nislamovs/Hardware-htop/docs/arduino_ide.png

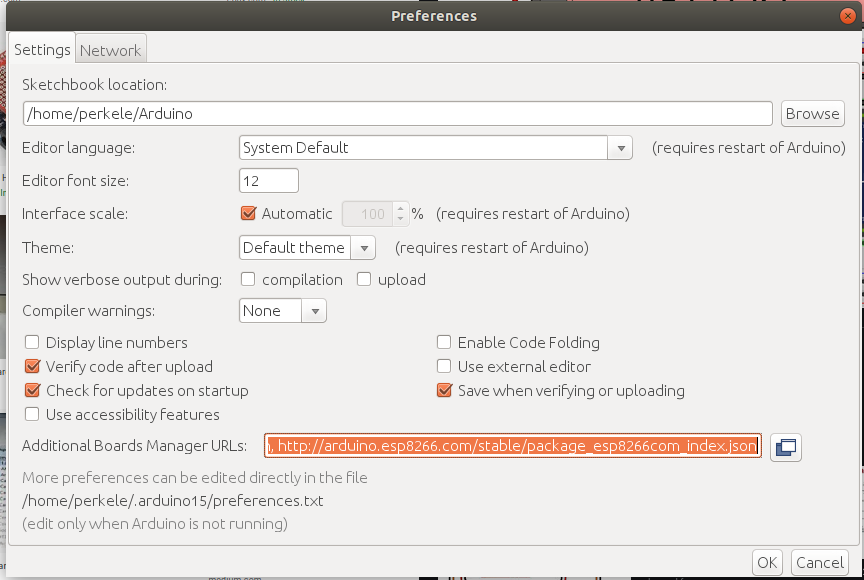
docs/arduino_ide.png
