nislamovs/Hardware-htop/docs/PURPOSE.JPG

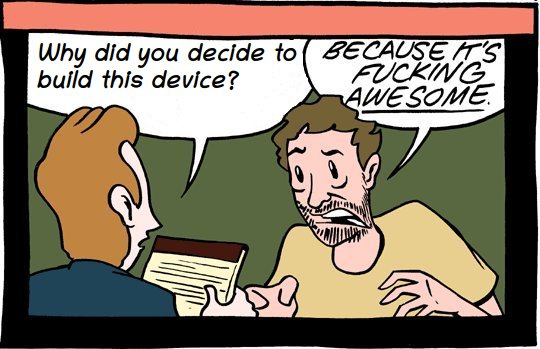
docs/PURPOSE.JPG
