nislamovs/Hardware-htop/front_panel_images/Core_01_bottom.png

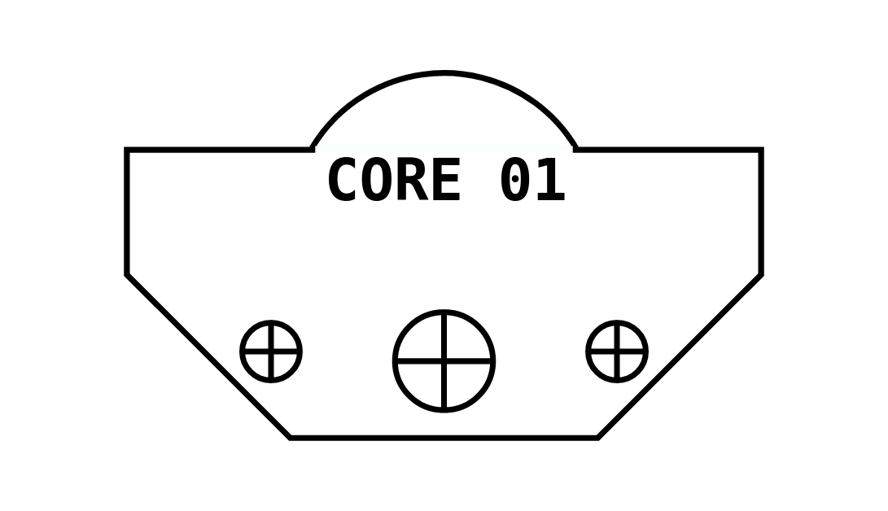
front_panel_images/Core_01_bottom.png
