nislamovs/Hardware-htop/front_panel_images/Core_all_top.png

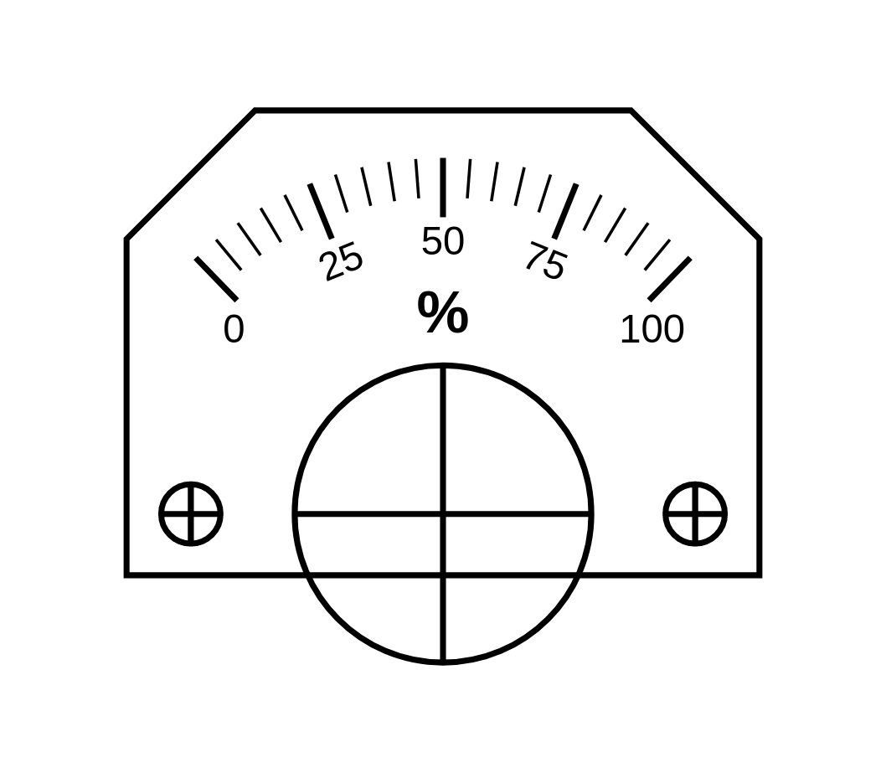
front_panel_images/Core_all_top.png
