nislamovs/Hardware-htop/front_panel_images/HDD.png

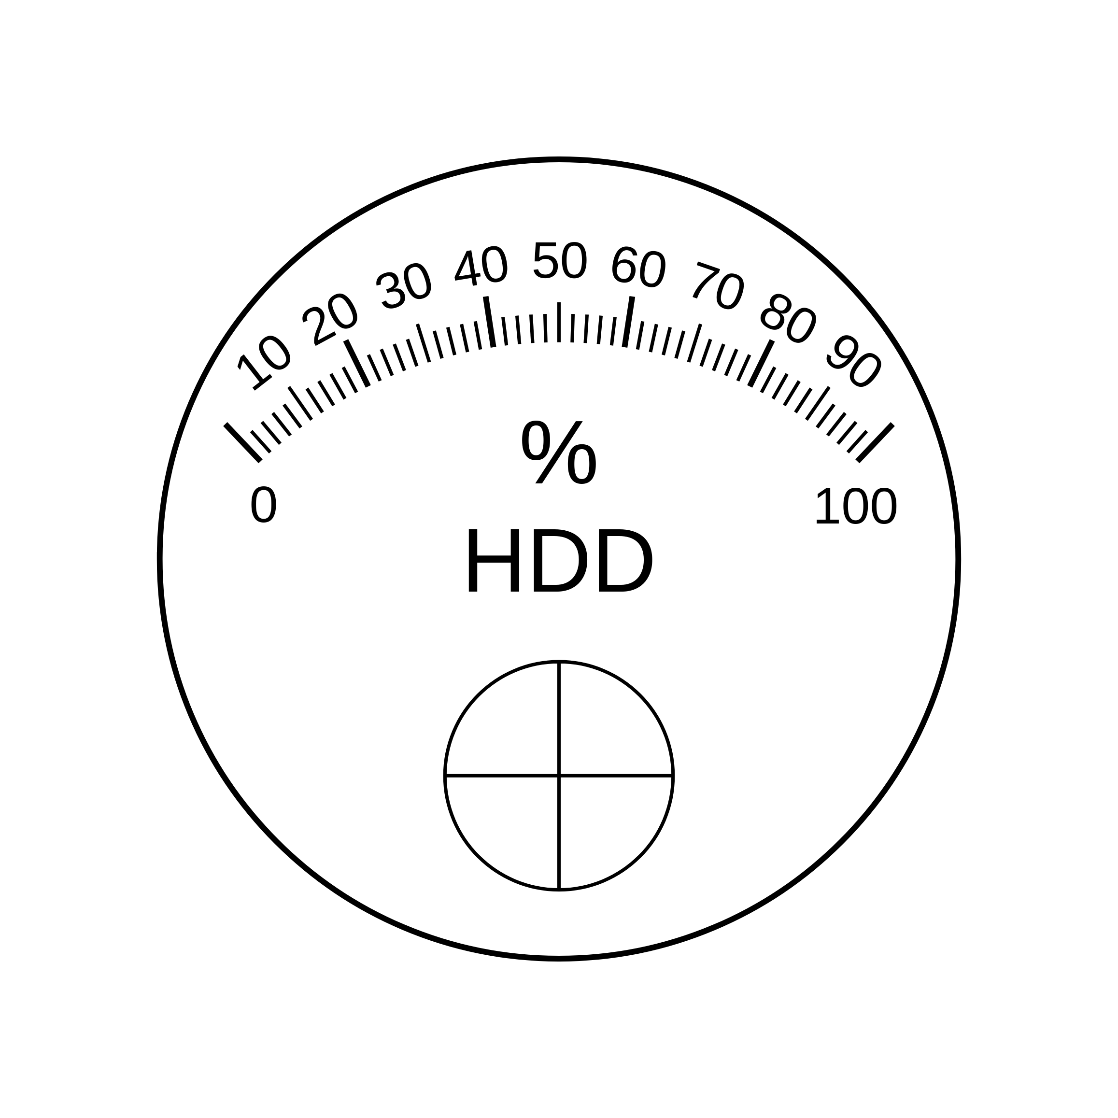
front_panel_images/HDD.png
